zrezke/anemometer/doc/img/IMG_20220907_160011.jpg

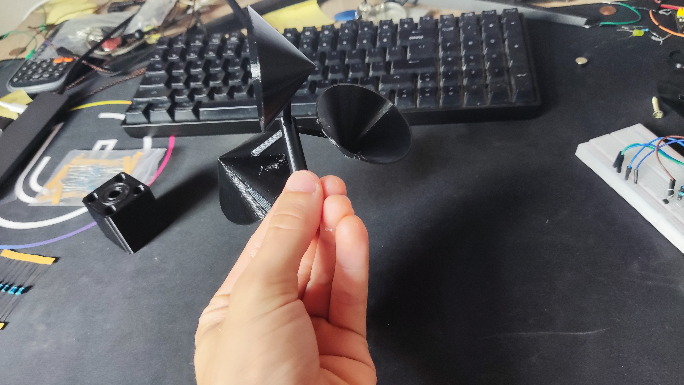
doc/img/IMG_20220907_160011.jpg
