zrezke/anemometer/doc/img/IMG_20220911_121213.jpg

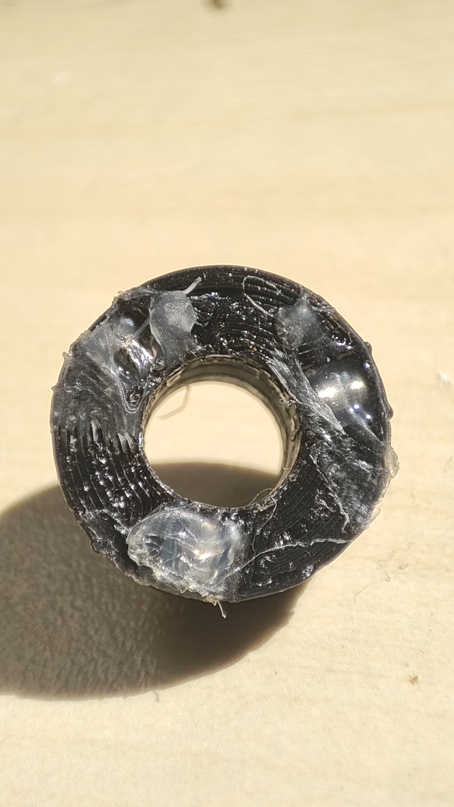
doc/img/IMG_20220911_121213.jpg
