zrezke/anemometer/doc/img/IMG_20220911_122543.jpg

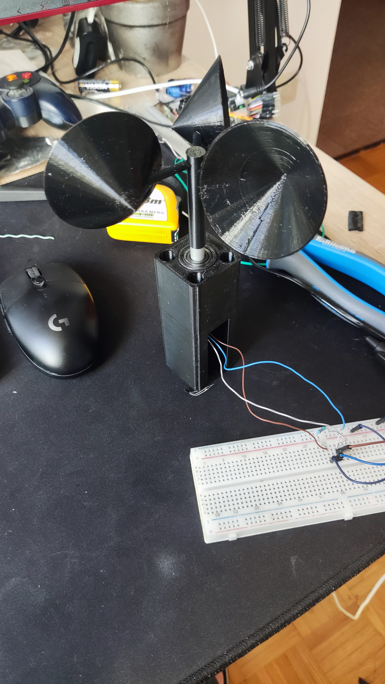
doc/img/IMG_20220911_122543.jpg
