zrezke/anemometer/doc/img/IMG_20220922_200802.jpg

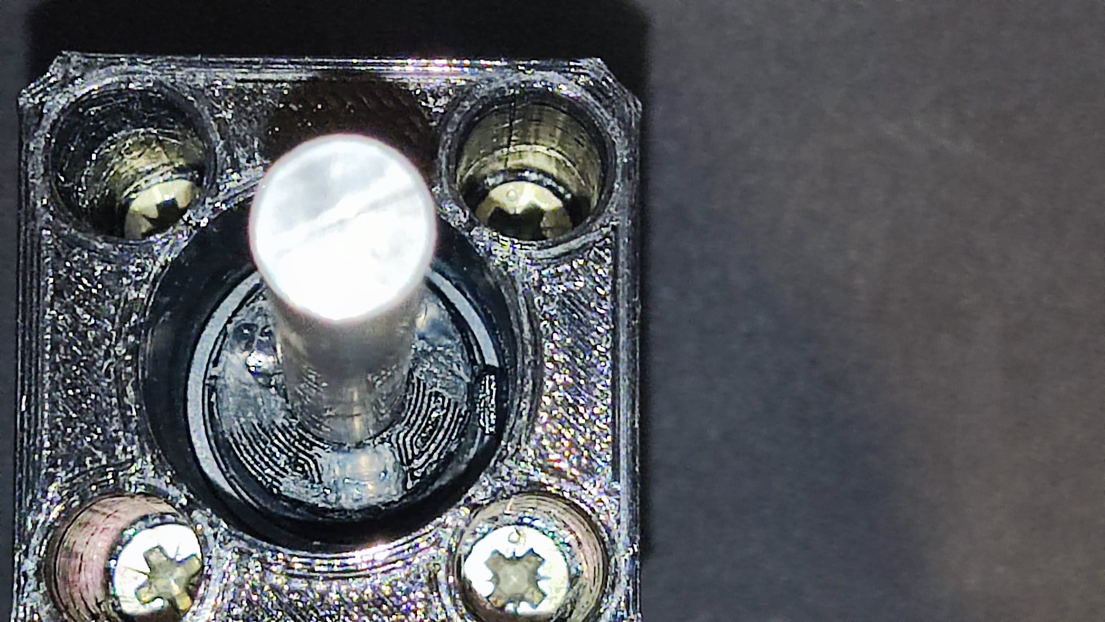
doc/img/IMG_20220922_200802.jpg
