zrezke/anemometer/firmware/main/btle_gap.h

#define DEVICE_NAME "Anemometer V1"

typedef unsigned char uint8_t;

// True wind speed service uuid (0x2A70)
static uint8_t true_wind_speed_service_uuid[16] = {
    // LSB <---> MSB
    0x2A, 0x70, 0x00, 0x00, 0x00, 0x00, 0x00, 0x00, 0x00, 0x00, 0x00, 0x00, 0x00, 0x00, 0x00, 0x00};

static esp_ble_adv_data_t anemometer_adv_config = {
    .set_scan_rsp = false,
    .include_name = true,
    .include_txpower = true,
    .min_interval = 0x0006,
    .max_interval = 0x0010,
    .appearance = 0x00,
    .manufacturer_len = 0,       // TEST_MANUFACTURER_DATA_LEN,
    .p_manufacturer_data = NULL, //&test_manufacturer[0],
    .service_data_len = 0,
    .p_service_data = NULL,
    .service_uuid_len = sizeof(true_wind_speed_service_uuid),
    .p_service_uuid = true_wind_speed_service_uuid,
    .flag = (ESP_BLE_ADV_FLAG_GEN_DISC | ESP_BLE_ADV_FLAG_BREDR_NOT_SPT)};

static esp_ble_adv_params_t anemometer_adv_params = {
    .adv_int_min = 0x20,
    .adv_int_max = 0x40,
    .adv_type = ADV_TYPE_IND,
    .own_addr_type = BLE_ADDR_TYPE_PUBLIC,
    //.peer_addr            =
    //.peer_addr_type       =
    .channel_map = ADV_CHNL_ALL,
    .adv_filter_policy = ADV_FILTER_ALLOW_SCAN_ANY_CON_ANY,
};
